20khzdesign/batshield/spice/kk.cir

Examplex

v1 1 0 sin(0 1 1k 0 0) 
rload 1 0 10k 
